adamjvr/kimchi-HiFi-lid/PCB - SGTL/3D/54-00176.STEP

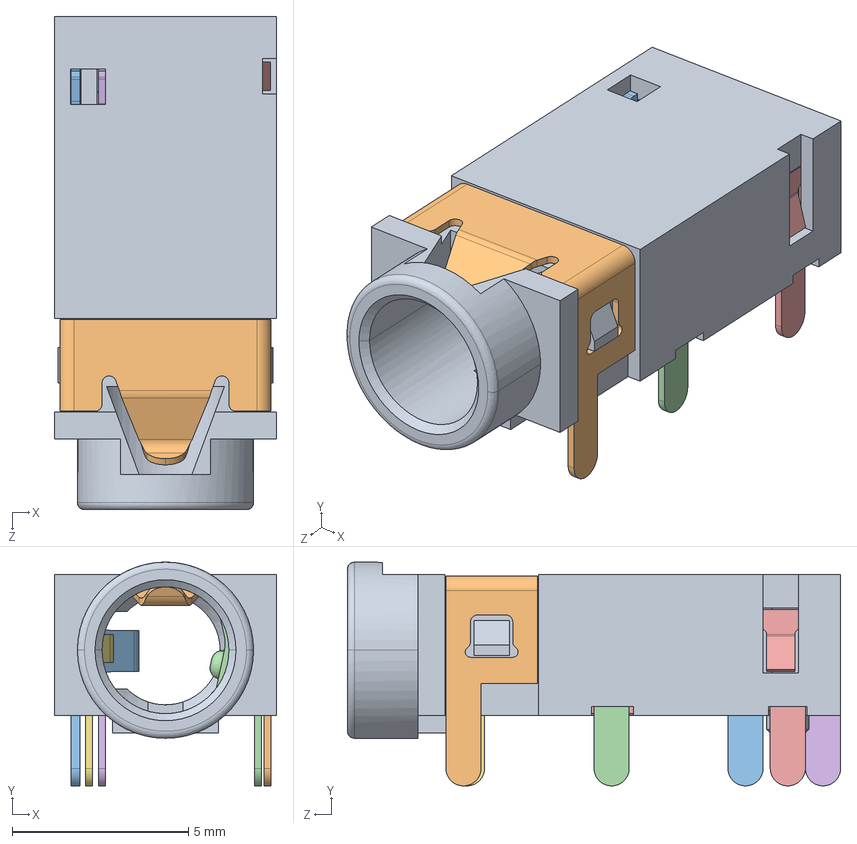
[picture p15: CAD file, 2020-12-16]
PCB - SGTL/3D/54-00176.STEP
6.30 x 6.35 x 14.0 mm
54-00176_insulator
54-00176_#1
54-00176_#4
54-00176_#3
54-00176_#6
54-00176_#5
54-00176_#2
