adamjvr/kimchi-HiFi-lid/PCB - SGTL/3D/CUI_DEVICES_RCJ-2123.step

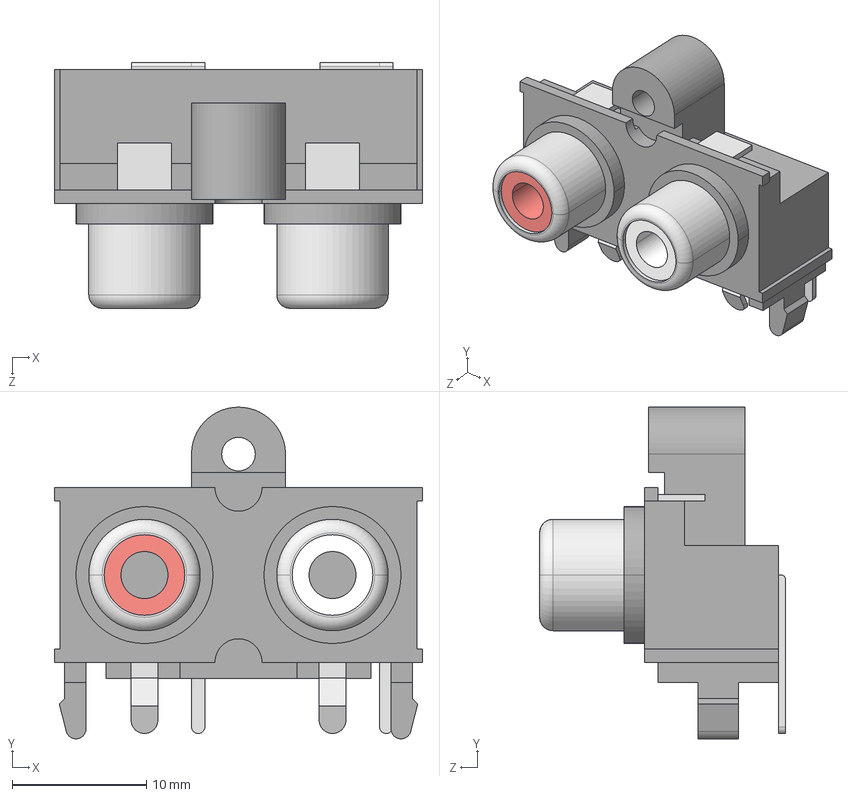
[picture p16: CAD file, 2020-12-16]
PCB - SGTL/3D/CUI_DEVICES_RCJ-2123.step
27.4 x 24.7 x 18.3 mm
RCJ-21_RCJ-21XX
PLUG_Red
PLUG_White
