adamjvr/kimchi-HiFi-lid/PCB - SGTL/3D/SGTL5000XNLA3.STEP

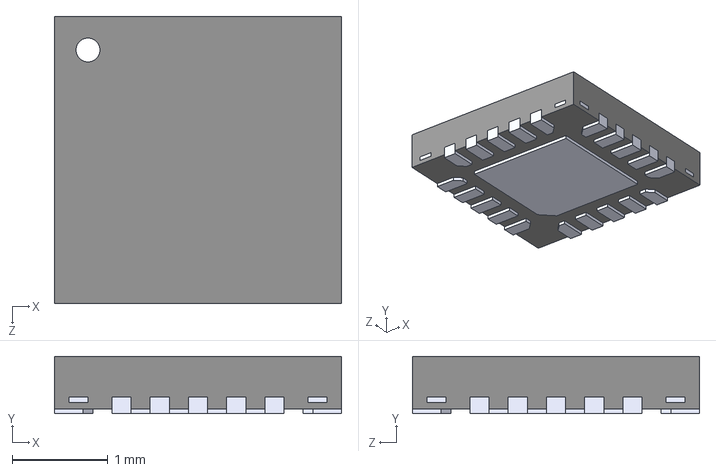
[picture p17: CAD file, 2020-12-16]
PCB - SGTL/3D/SGTL5000XNLA3.STEP
3.00 x 0.6 x 3.00 mm
